HuanYitiao/con-venience/ui/templates/fullscreen.jpg

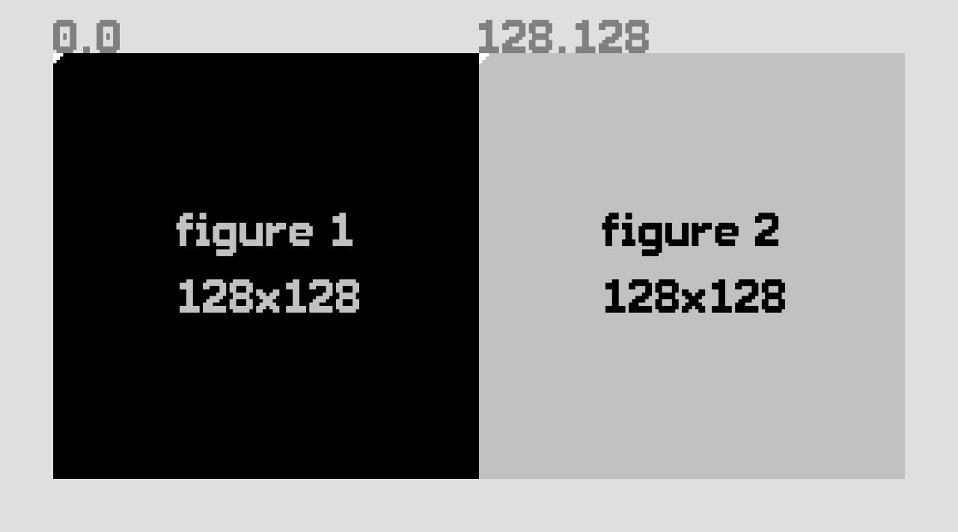
ui/templates/fullscreen.jpg
