HuanYitiao/con-venience/ui/templates/list_2.jpg

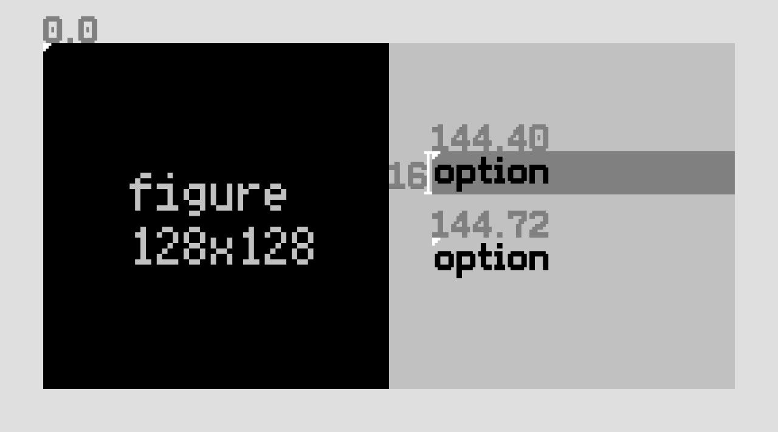
ui/templates/list_2.jpg
