HuanYitiao/con-venience/ui/templates/list_4.jpg

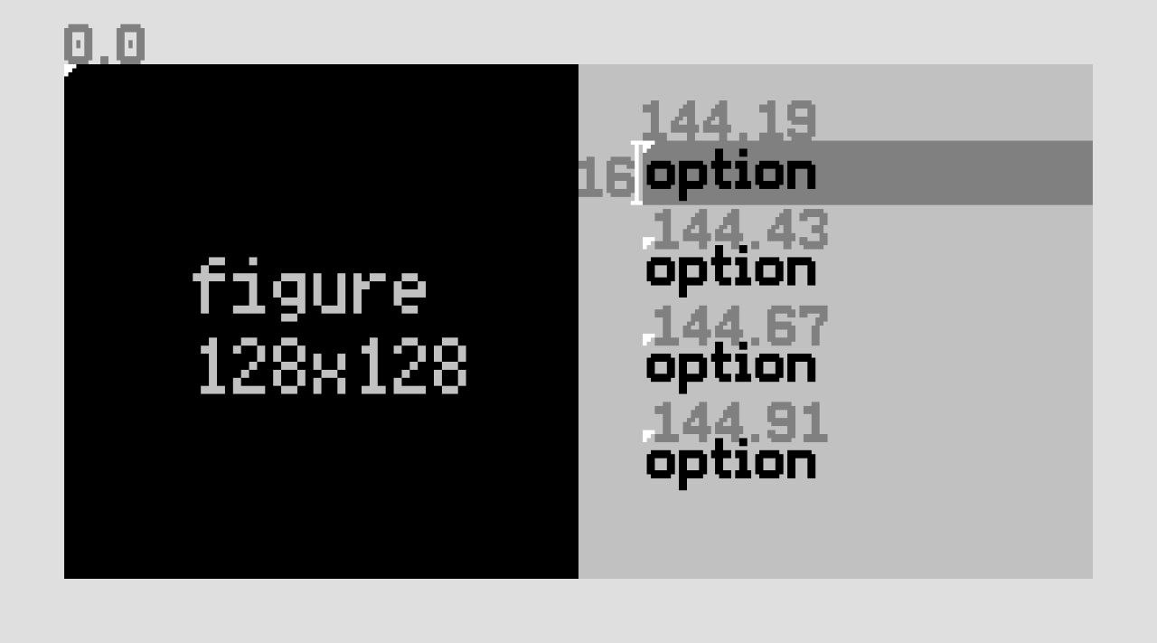
ui/templates/list_4.jpg
