HuanYitiao/con-venience/ui/templates/list_5.jpg

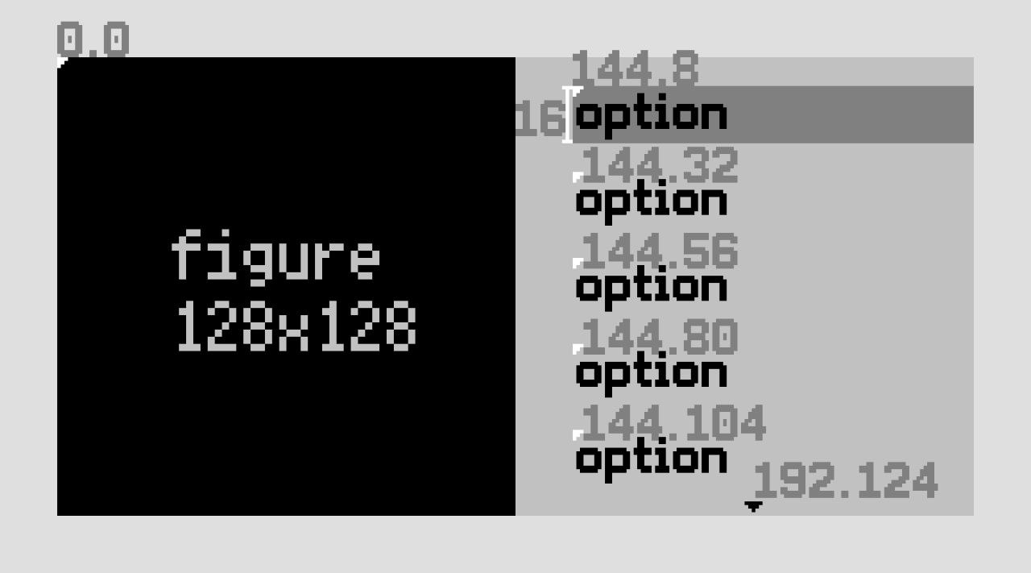
ui/templates/list_5.jpg
